brushyfork23/kitchen_lights/3d/solidworks/HPC port.SLDPRT

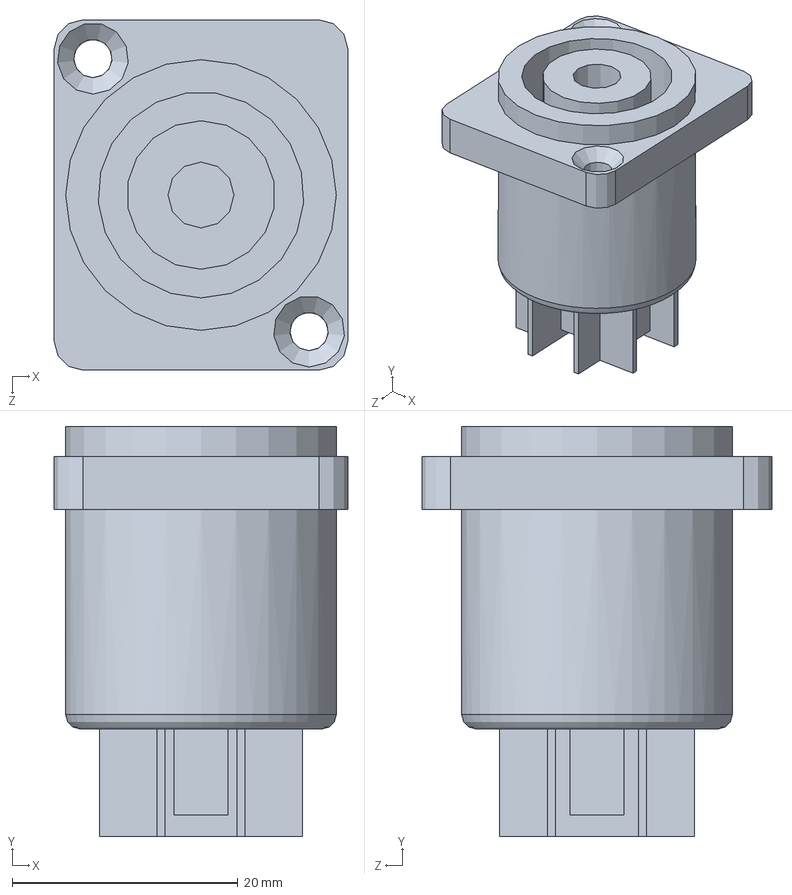
[picture p25: CAD file, 2020-08-09]
3d/solidworks/HPC port.SLDPRT
26.0 x 36.3 x 31.0 mm
