brushyfork23/kitchen_lights/3d/solidworks/light sensro.SLDPRT

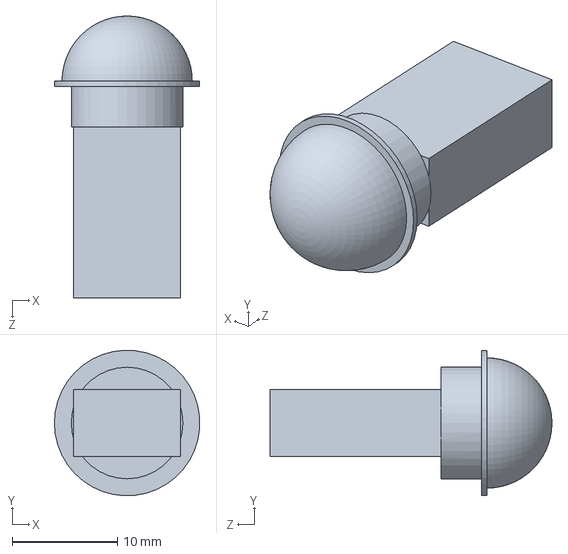
[picture p26: CAD file, 2020-08-09]
3d/solidworks/light sensro.SLDPRT
13.8 x 13.8 x 26.8 mm
