brushyfork23/kitchen_lights/3d/solidworks/photocell.SLDPRT

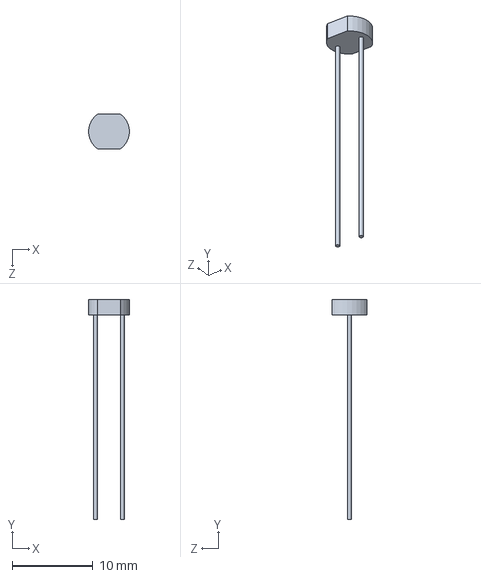
[picture p27: CAD file, 2020-08-09]
3d/solidworks/photocell.SLDPRT
5.05 x 27.3 x 4.37 mm
