brushyfork23/kitchen_lights/3d/solidworks/terminal block - 8 pos 15A.SLDPRT

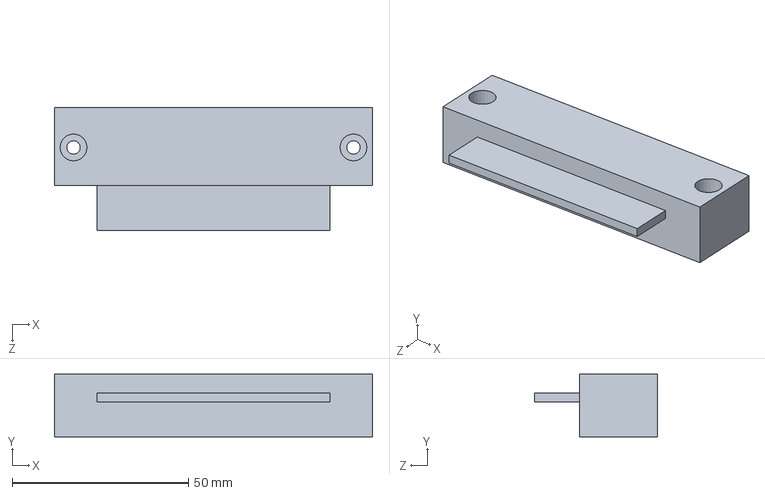
[picture p28: CAD file, 2020-08-09]
3d/solidworks/terminal block - 8 pos 15A.SLDPRT
90.2 x 17.8 x 34.8 mm
