brushyfork23/kitchen_lights/3d/solidworks/pushbutton.SLDPRT

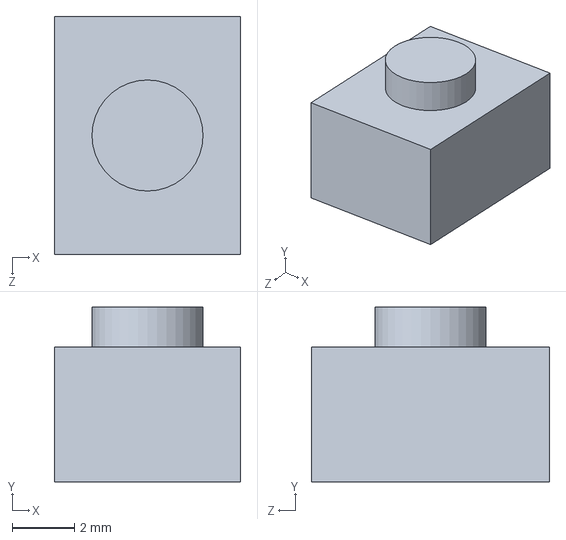
[picture p29: CAD file, 2020-08-09]
3d/solidworks/pushbutton.SLDPRT
5.97 x 5.59 x 7.62 mm
