brushyfork23/kitchen_lights/3d/solidworks/PIR sensor.SLDPRT

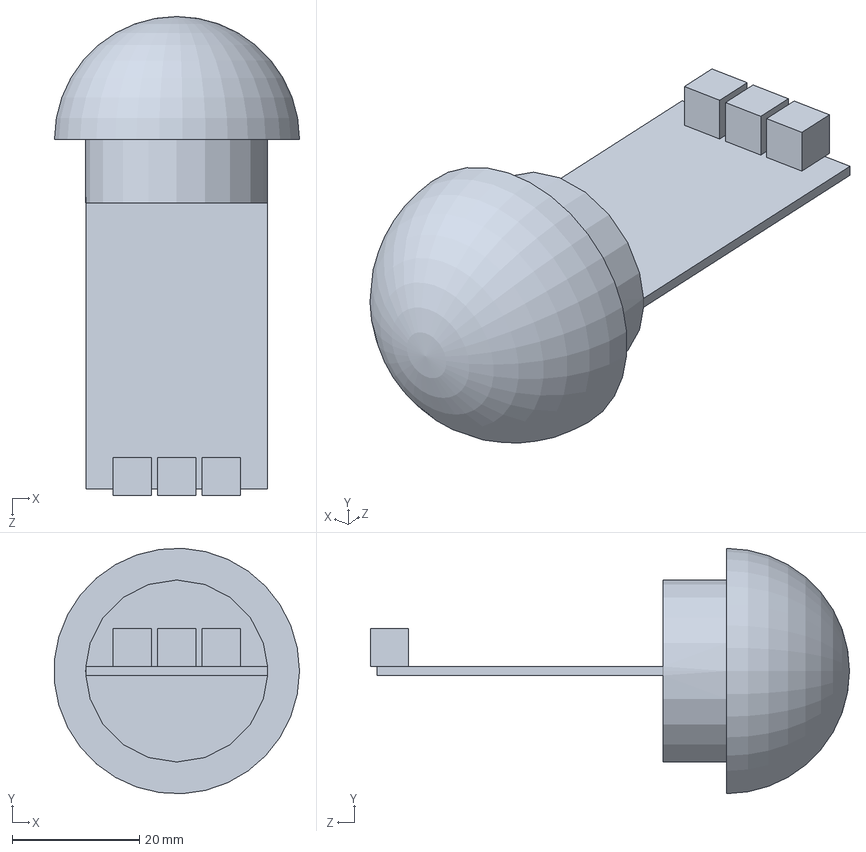
[picture p30: CAD file, 2020-08-09]
3d/solidworks/PIR sensor.SLDPRT
38.5 x 38.6 x 75.3 mm
