brushyfork23/kitchen_lights/3d/solidworks/terminal block - 5 pos 25A.SLDPRT

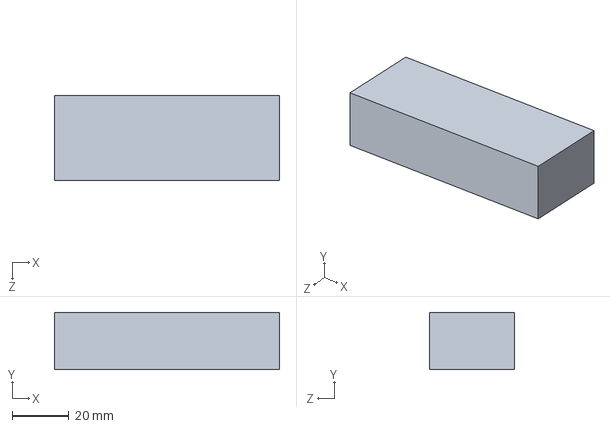
[picture p31: CAD file, 2020-08-09]
3d/solidworks/terminal block - 5 pos 25A.SLDPRT
79.0 x 20.1 x 30.0 mm
