brushyfork23/kitchen_lights/3d/solidworks/SP105E LED controller.SLDPRT

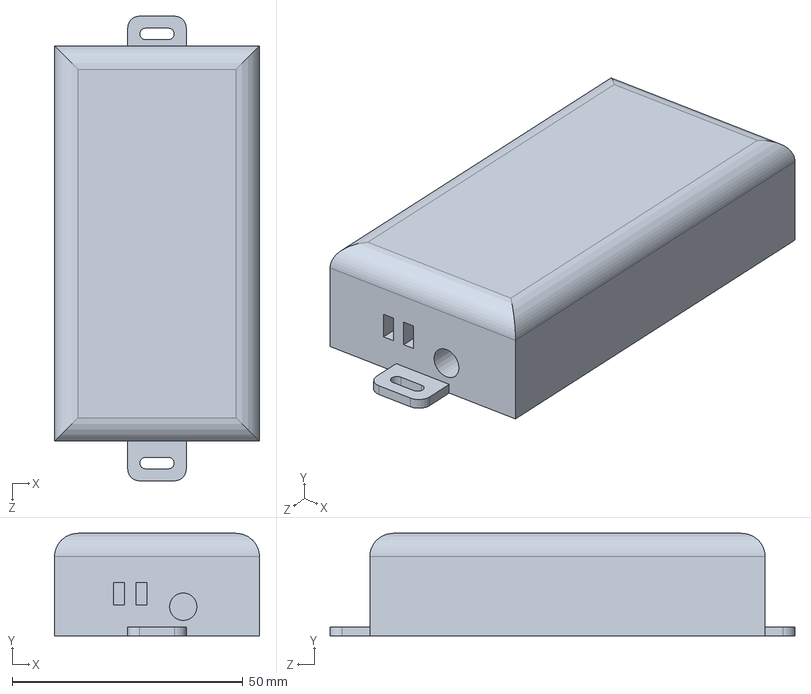
[picture p32: CAD file, 2020-08-09]
3d/solidworks/SP105E LED controller.SLDPRT
44.5 x 22.2 x 100.8 mm
