brushyfork23/kitchen_lights/3d/solidworks/circuit board.SLDPRT

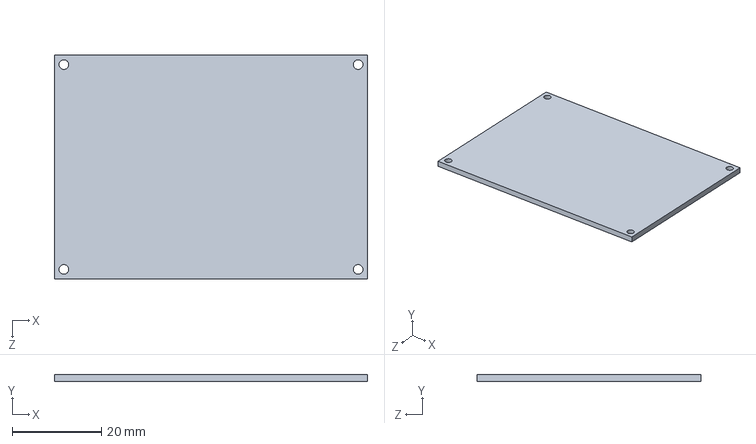
[picture p33: CAD file, 2020-08-09]
3d/solidworks/circuit board.SLDPRT
70.0 x 1.64 x 50.0 mm
